fotis-karagiannis/esp32-tank-level-monitor/tankSensor/webpages.h

#ifndef WEBPAGES_H
#define WEBPAGES_H

/**
  Includes the webpages used in the application
*/

extern const char* wifiSetupPage;
extern const char* wifiSavedPage;
extern const char* dimensionsPage;
extern const char* dashboardPage;

#endif
